MYBLtd/Chaoticvolt-SensorHUB/src/certificates.h

#ifndef CERTIFICATES_H
#define CERTIFICATES_H

#include <pgmspace.h>

// ISRG Root X2 Certificate (Let's Encrypt)
static const char let_encrypt_root_ca[] PROGMEM = R"EOF(
-----BEGIN CERTIFICATE-----
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
/q4AaOeMSQ+2b1tbFfLn
-----END CERTIFICATE-----
)EOF";

#endif
